SaifSabban/MiniTV/Extra/1.JPG

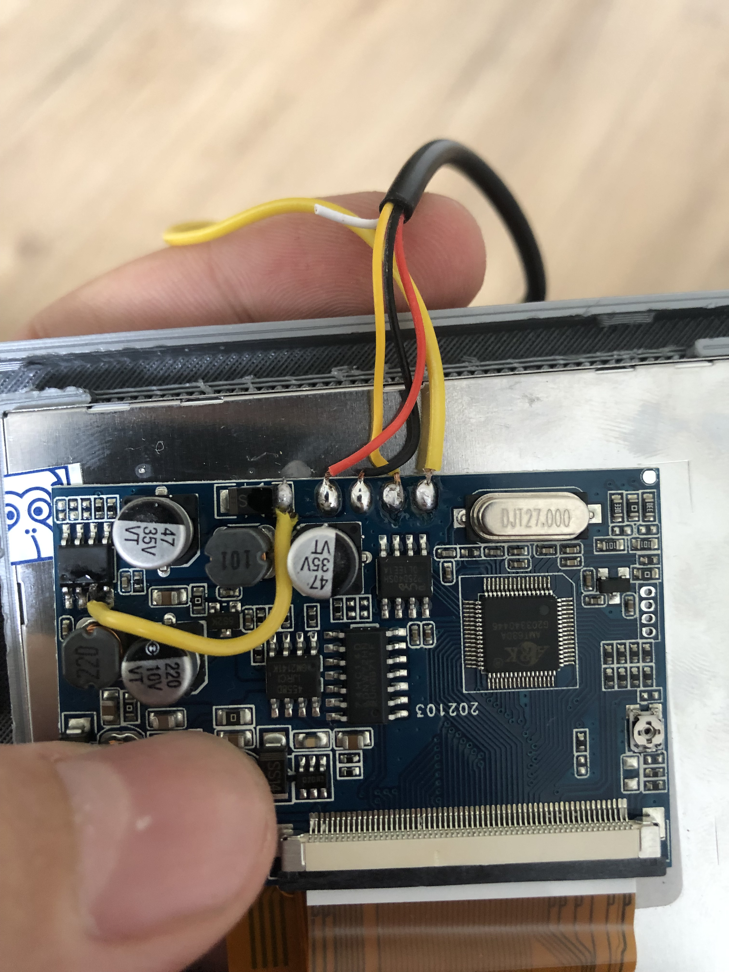
Extra/1.JPG
