SaifSabban/MiniTV/Extra/2.JPG

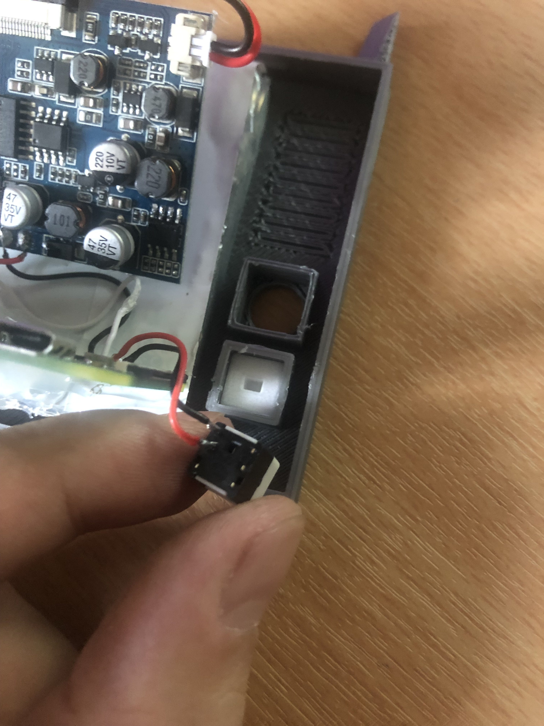
Extra/2.JPG
