SaifSabban/MiniTV/Extra/3.JPG

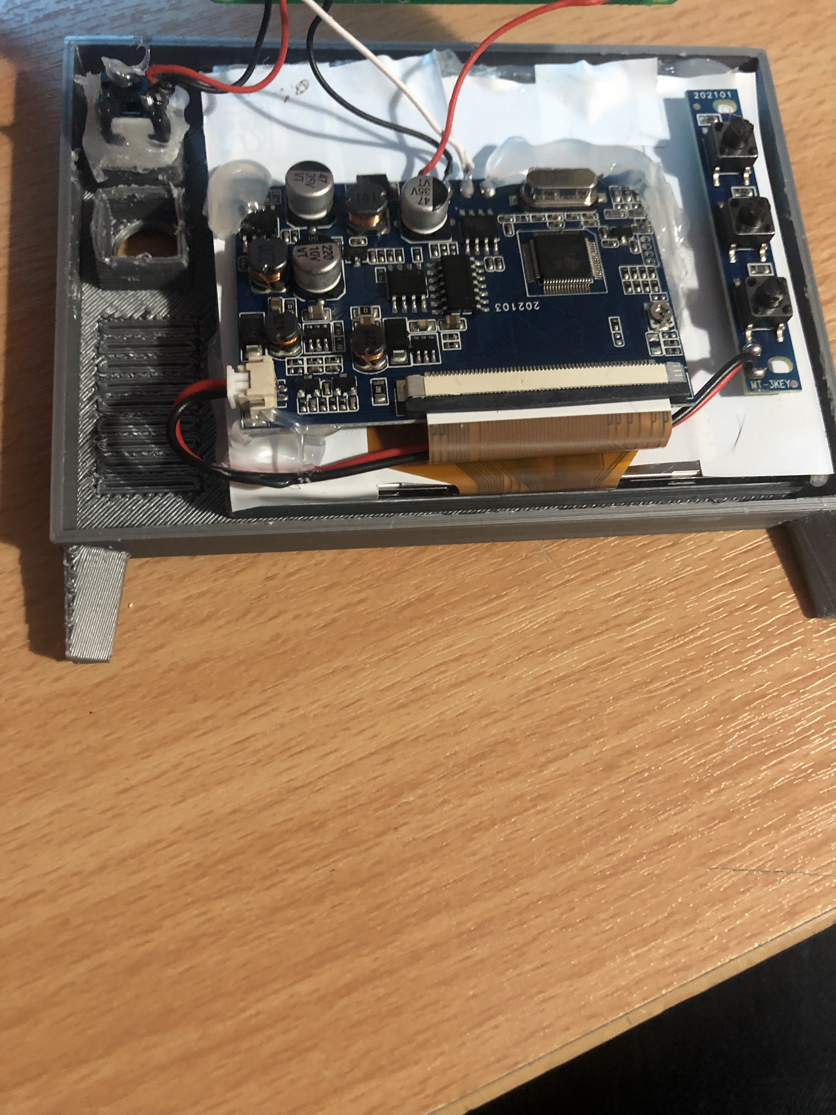
Extra/3.JPG
