SaifSabban/MiniTV/Extra/5.JPG

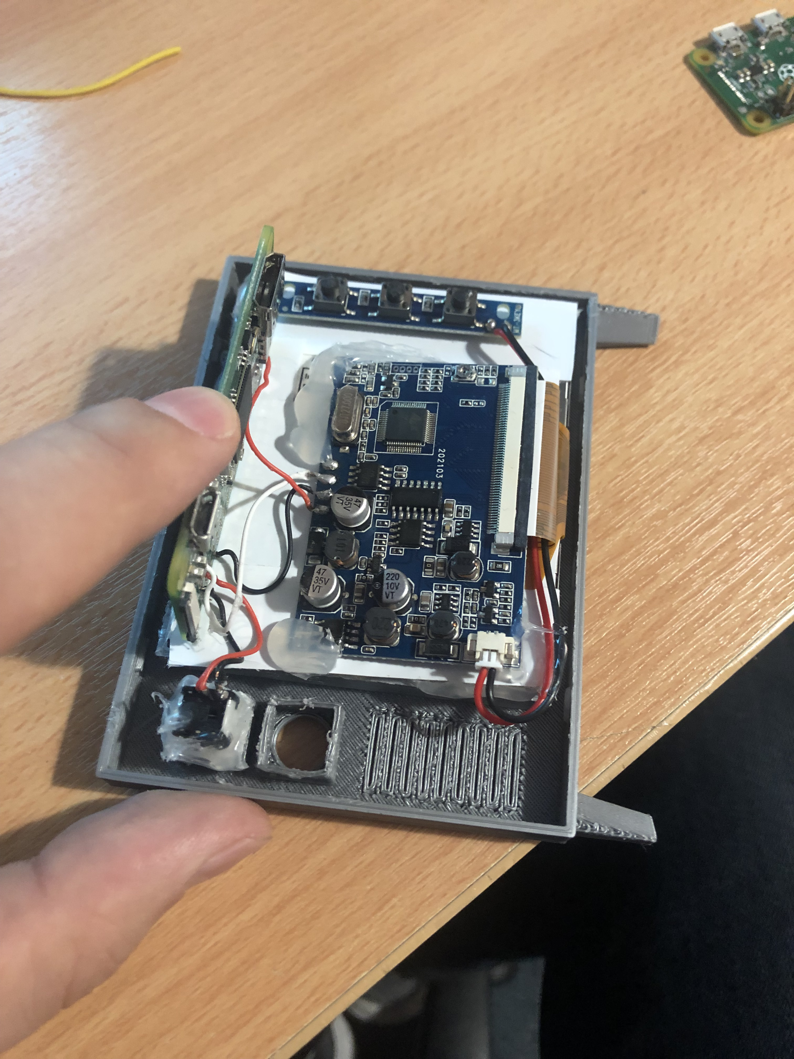
Extra/5.JPG
