SaifSabban/MiniTV/Extra/6.JPG

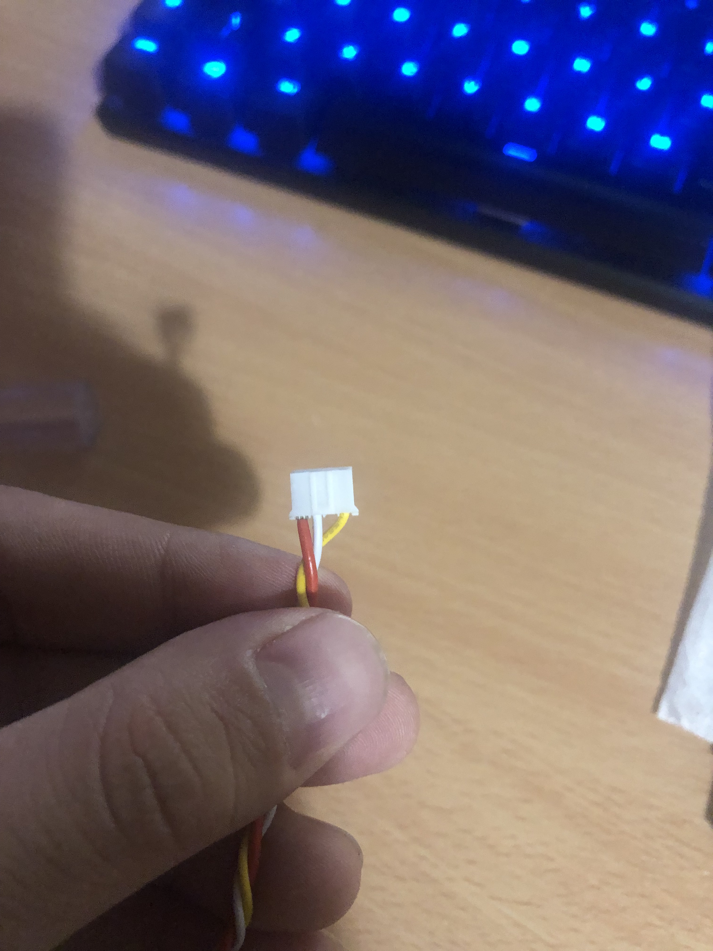
Extra/6.JPG
