SaifSabban/MiniTV/Extra/7.JPG

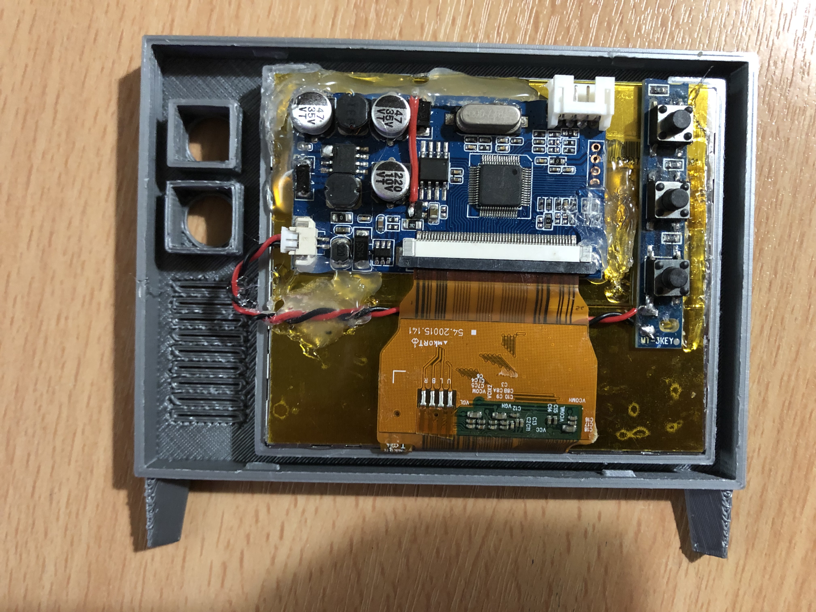
Extra/7.JPG
