SaifSabban/MiniTV/Extra/8.JPG

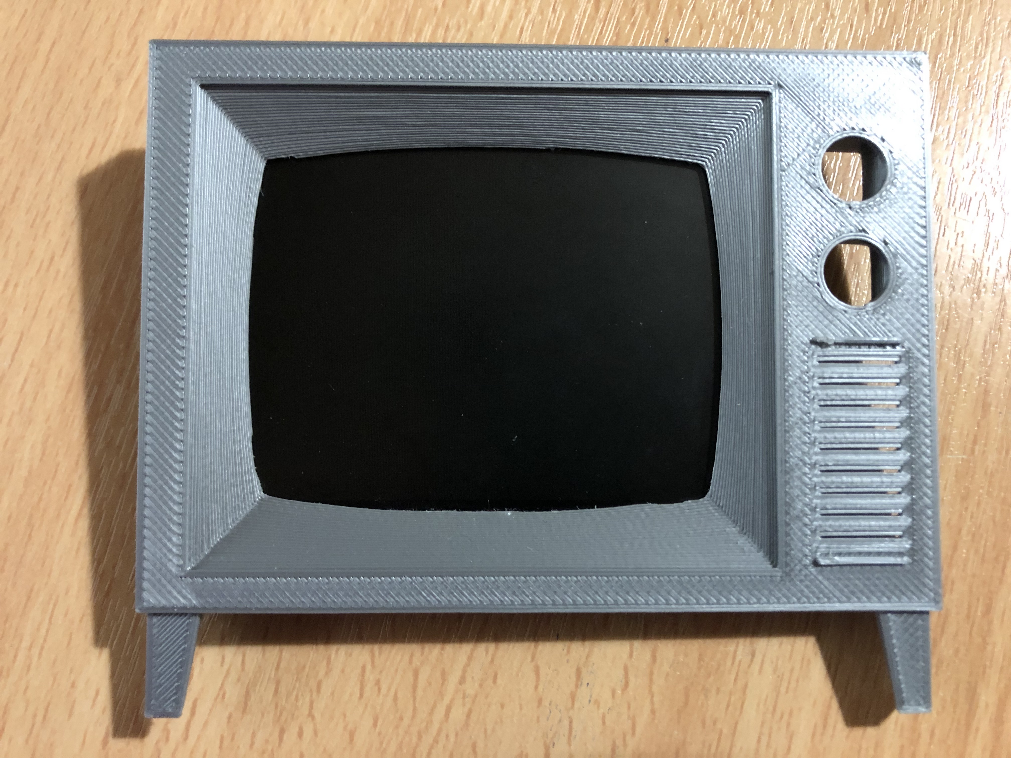
Extra/8.JPG
