SaifSabban/MiniTV/Extra/9.JPG

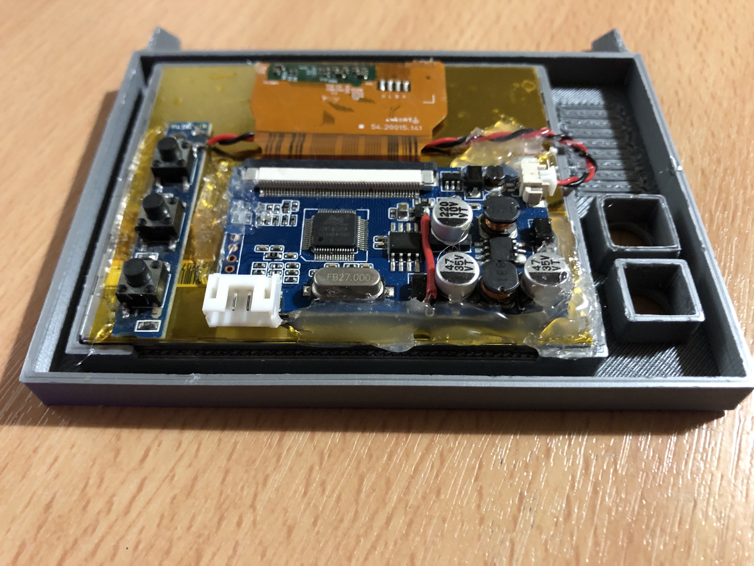
Extra/9.JPG
