SaifSabban/MiniTV/Extra/10.JPG

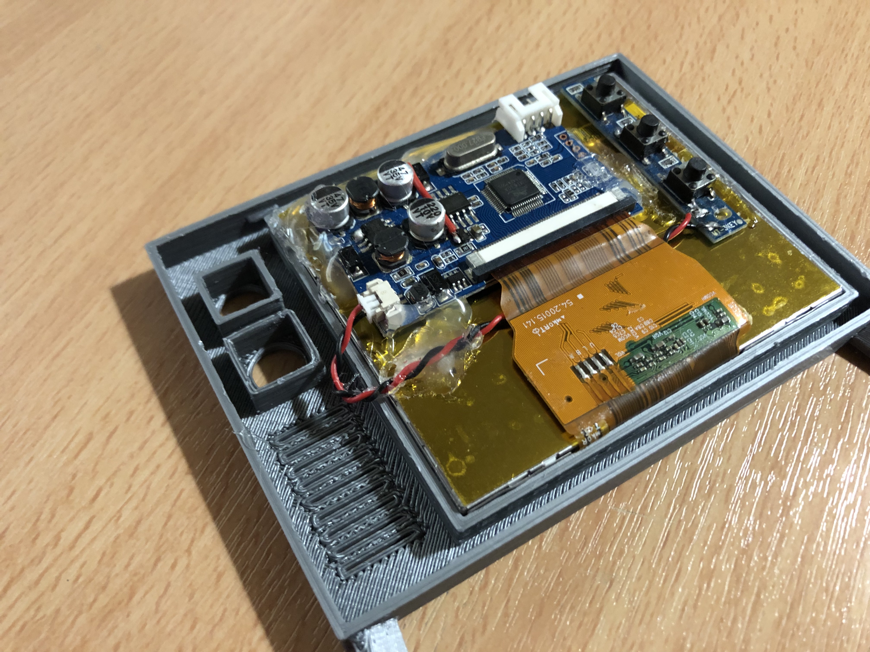
Extra/10.JPG
