SaifSabban/MiniTV/Extra/Speaker.jpg

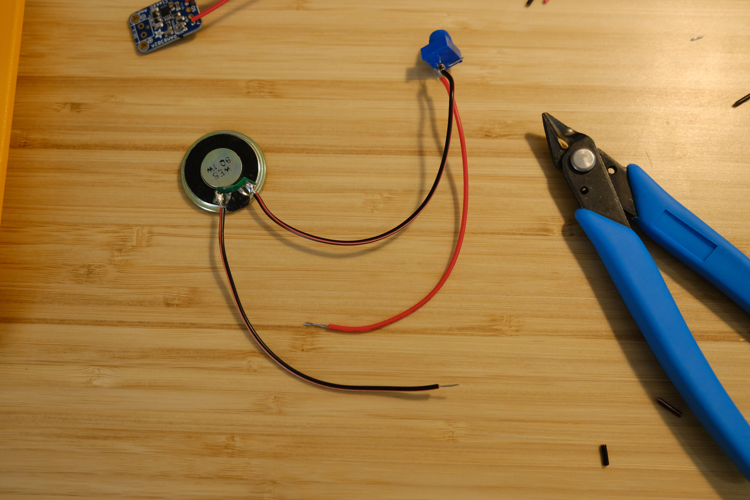
Extra/Speaker.jpg
